katafoxi/LARKeyboard/images/81.jpg

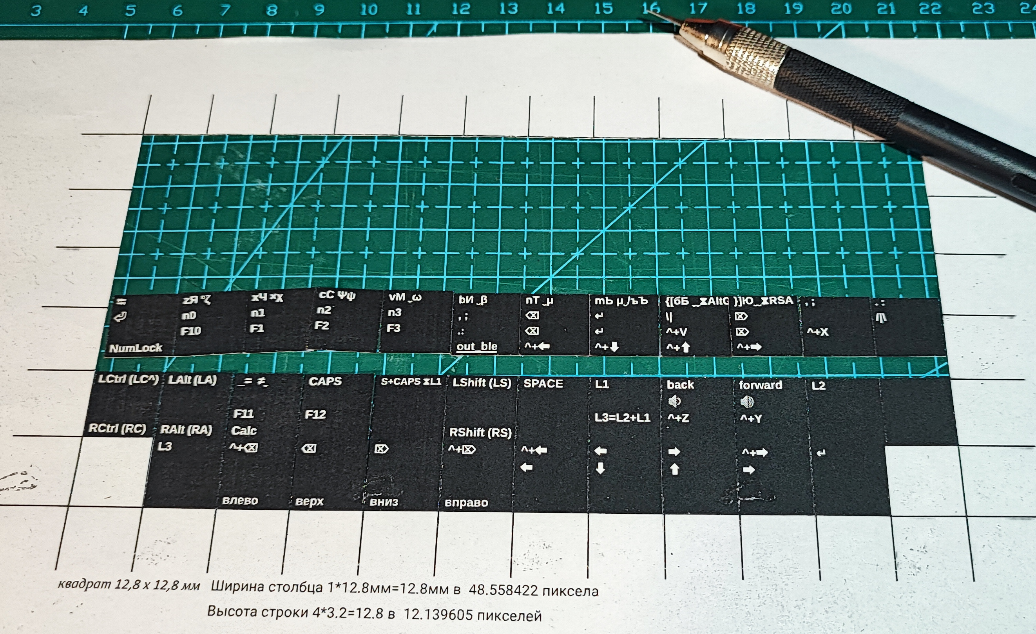
images/81.jpg
