katafoxi/LARKeyboard/images/92.jpg

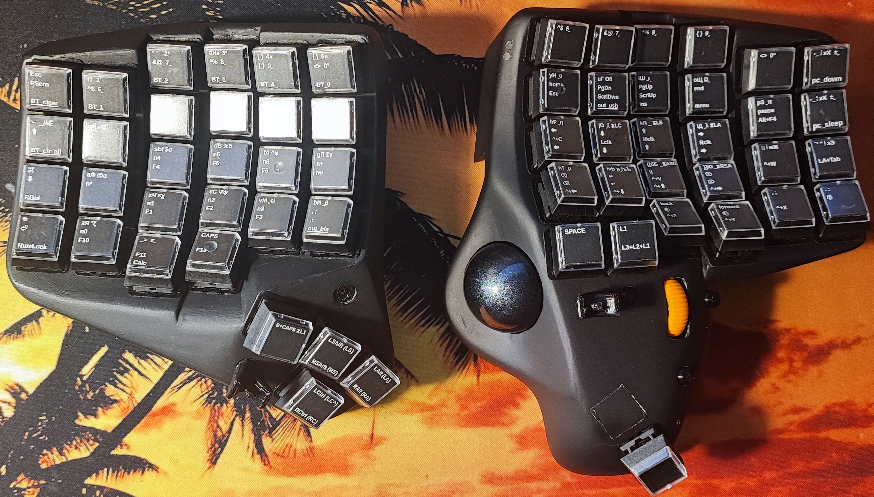
images/92.jpg
