katafoxi/LARKeyboard/images/_LARKeyboard.png

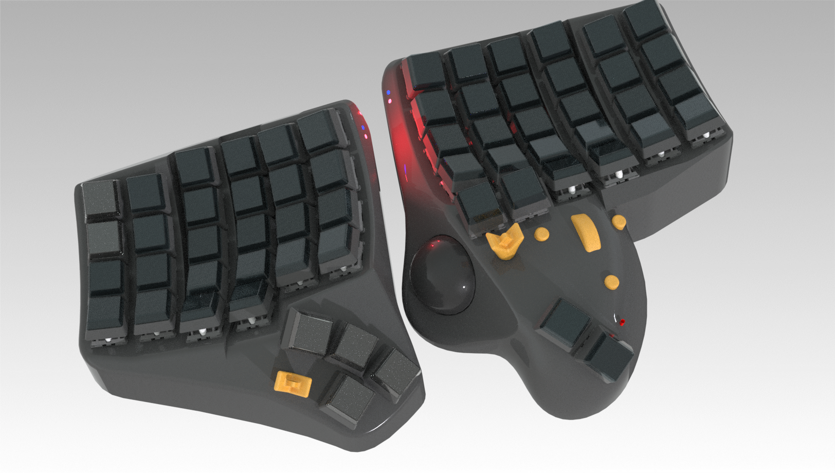
images/_LARKeyboard.png
